cmoore42/oscbox/code/i2c.h

#ifndef I2C_H
#define I2C_H

#include <stdint.h>

int i2c_open(int bus, int addr);
void i2c_init(int f);
uint32_t i2c_read(int f, int reg);
void i2c_write(int f, int reg, int value);

#define REG_IODIRA	0x00
#define REG_IODIRB	0x01
#define REG_IPOLA	0x02
#define REG_IPOLB	0x03
#define REG_GPINTENA	0x04
#define REG_GPINTENB	0x05
#define REG_DEFVALA	0x06
#define REG_DEFVALB	0x07
#define REG_INTCONA	0x08
#define REG_INTCONB	0x09
#define REG_IOCON	0x0a
#define REG_GPPUA	0x0c
#define REG_GPPUB	0x0d
#define REG_INTFA	0x0e
#define REG_INTFB	0x0f
#define REG_INTCAPA	0x10
#define REG_INTCAPB	0x11
#define REG_GPIOA	0x12
#define REG_GPIOB	0x13
#define REG_OLATA	0x14
#define REG_OLATB	0x15


#endif
